ubis/bmwcanmodule/firmware/bmwcanmodule.X/version.h

/* 
 * File:   version.h  
 * Author: Jokubas Maciulaitis (ubis)
 * Date:   2022 02 16 
 */

#ifndef __VERSION_H__
#define	__VERSION_H__

#define FW_VERSION_MAJOR 0
#define FW_VERSION_MINOR 1

#endif	// __VERSION_H__
